schultzlab/ultra-cheap-light-field-microscope/Objective lens/UC2_20_focus_inlet_objective_mount_v8_30-200-240-266 v8.stl

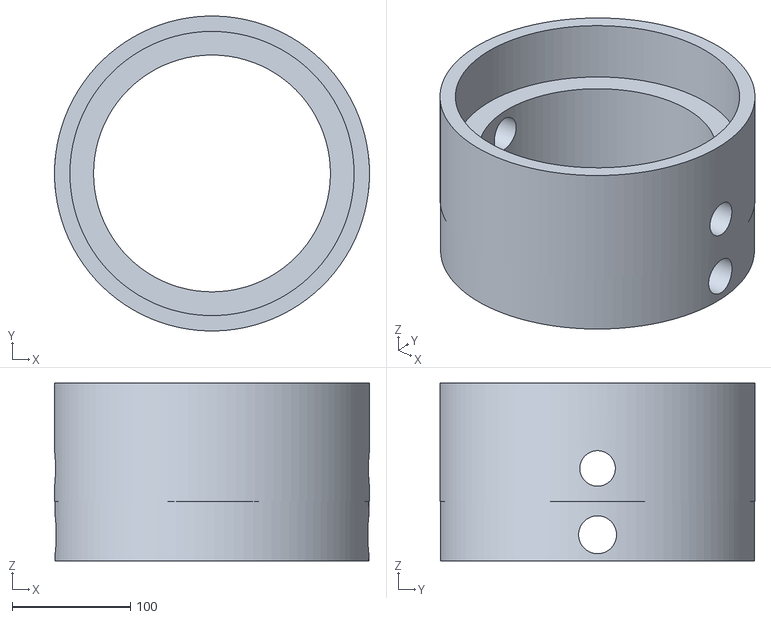
[picture p20: CAD file, 2021-07-01]
Objective lens/UC2_20_focus_inlet_objective_mount_v8_30-200-240-266 v8.stl
266.0 x 265.9 x 150.0
