schultzlab/ultra-cheap-light-field-microscope/Camera and relay lens/Cube Lid_2x1_-0.2mm with 5mm holes on one side face v1.stl

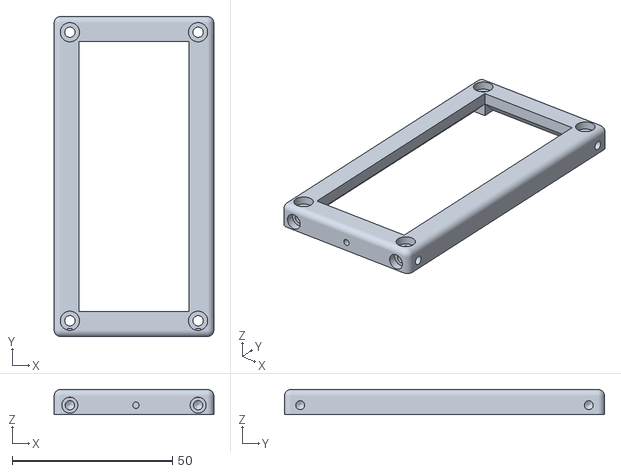
[picture p21: CAD file, 2021-07-01]
Camera and relay lens/Cube Lid_2x1_-0.2mm with 5mm holes on one side face v1.stl
49.8 x 99.8 x 7.80
