schultzlab/ultra-cheap-light-field-microscope/MLA/20_Insert_Lens_holder_v3_100mm.stl

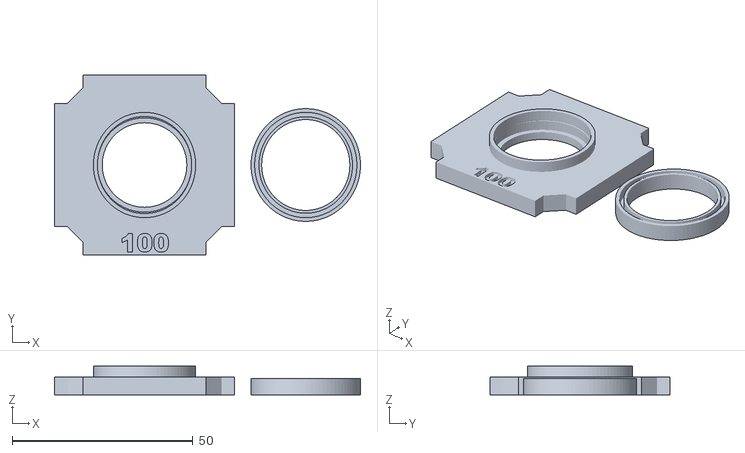
[picture p22: CAD file, 2021-07-01]
MLA/20_Insert_Lens_holder_v3_100mm.stl
84.6 x 49.8 x 8.00
