schultzlab/ultra-cheap-light-field-microscope/Modified UC2/cube for z ascii.stl

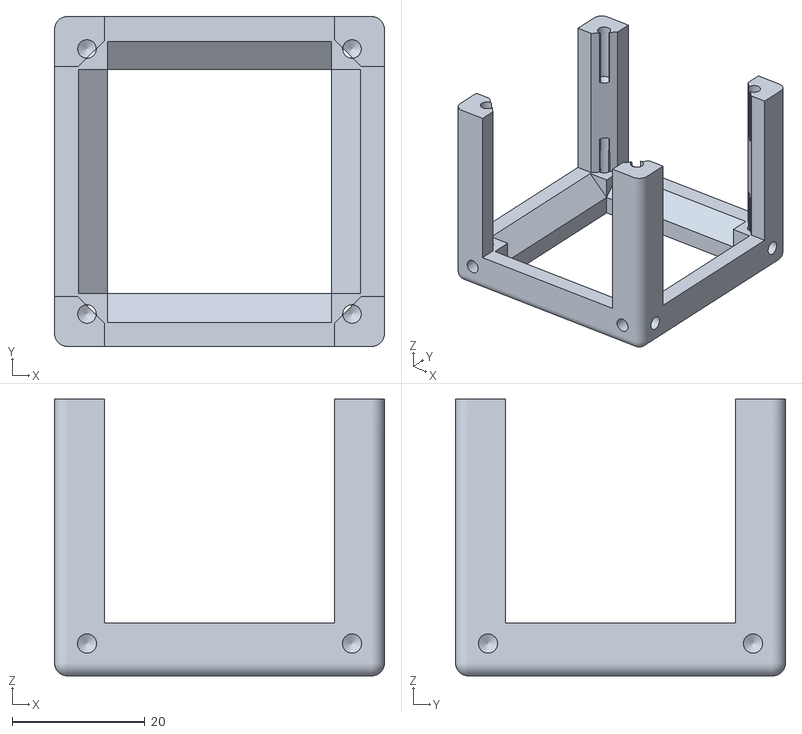
[picture p23: CAD file, 2021-07-01]
Modified UC2/cube for z ascii.stl
49.8 x 49.8 x 41.8
