schultzlab/ultra-cheap-light-field-microscope/Shortpass filter/Cube Lid_1x1 -0.1 v3.stl

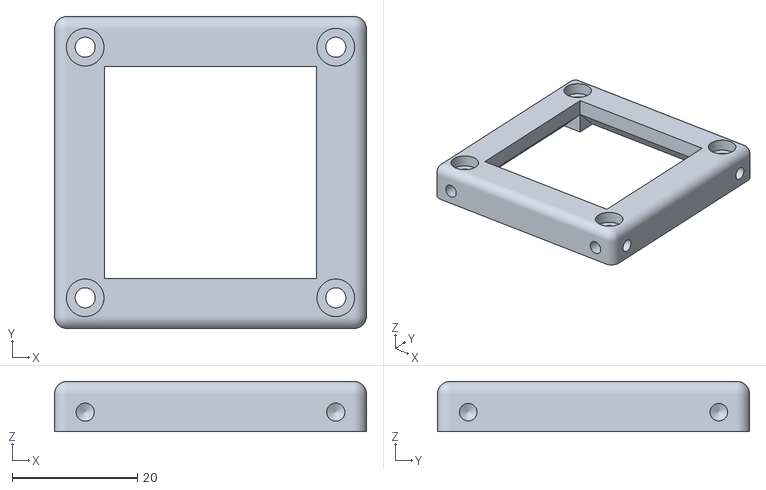
[picture p24: CAD file, 2021-07-01]
Shortpass filter/Cube Lid_1x1 -0.1 v3.stl
49.8 x 49.8 x 8.00
