schultzlab/ultra-cheap-light-field-microscope/Modified UC2/UC2_20_focus_inlet_objective_mount_v8_208-249-265 v2.stl

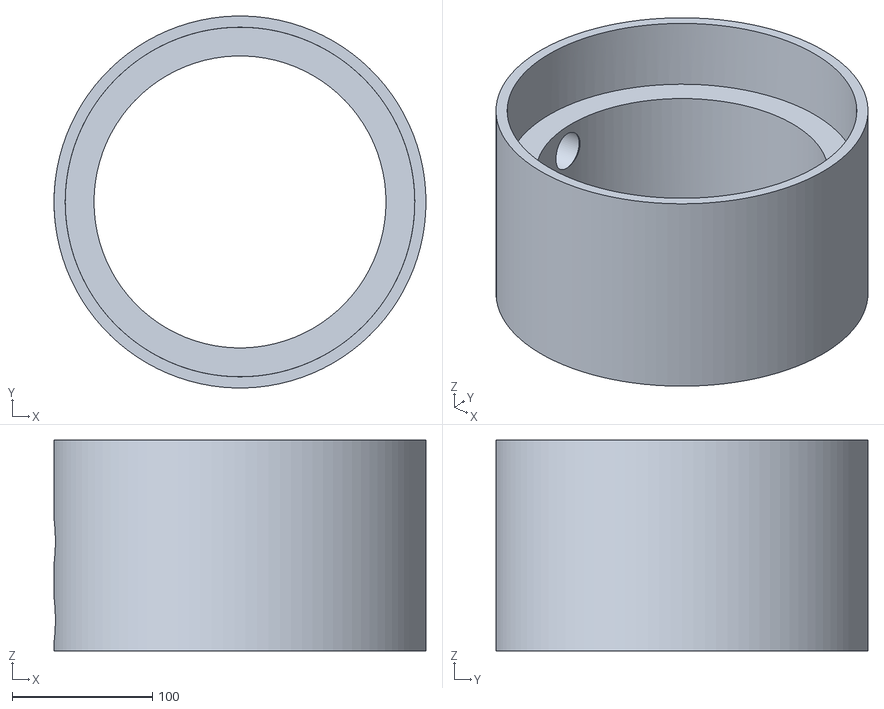
[picture p25: CAD file, 2021-07-01]
Modified UC2/UC2_20_focus_inlet_objective_mount_v8_208-249-265 v2.stl
265.0 x 264.9 x 150.0
