schultzlab/ultra-cheap-light-field-microscope/Objective lens/20_focus_inlet_linearflexure_v1_Adjusted 0.4mm v1.stl

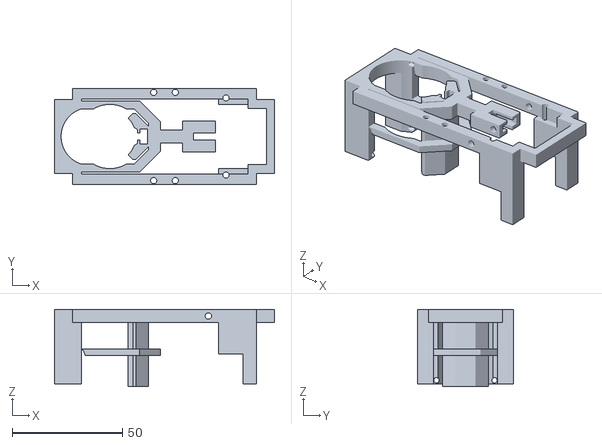
[picture p26: CAD file, 2021-07-01]
Objective lens/20_focus_inlet_linearflexure_v1_Adjusted 0.4mm v1.stl
99.8 x 43.6 x 35.0
