schultzlab/ultra-cheap-light-field-microscope/Own new parts/45 mirror_without_hole v3.stl

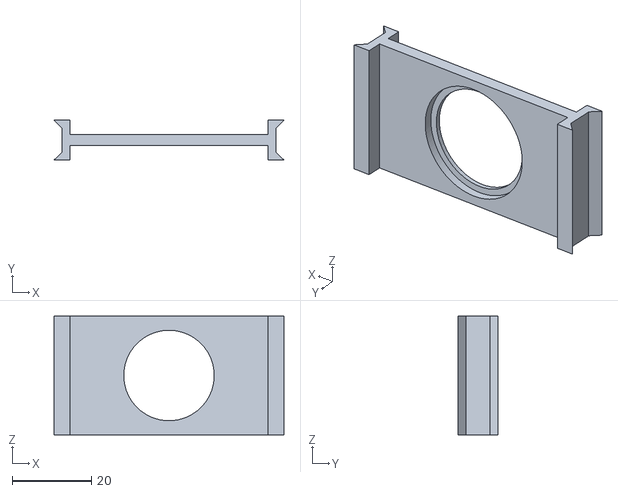
[picture p27: CAD file, 2021-07-01]
Own new parts/45 mirror_without_hole v3.stl
58.1 x 10.1 x 30.0
