schultzlab/ultra-cheap-light-field-microscope/Tube lens/SM1V05-Solidworks body 25.85.STL

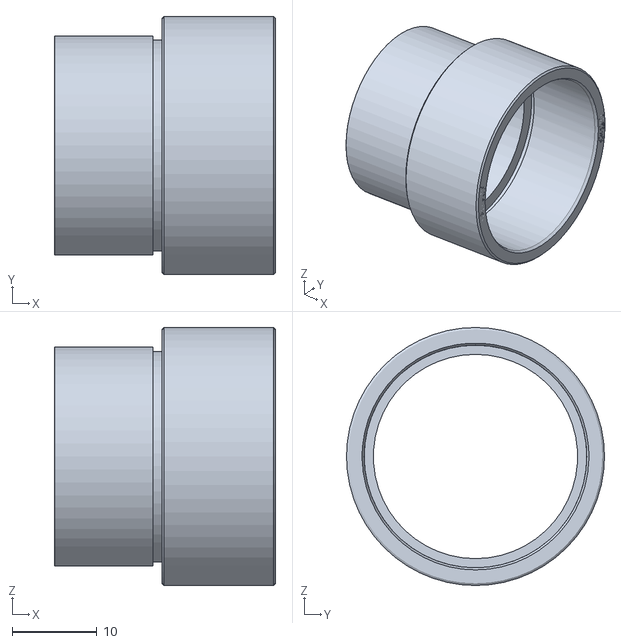
[picture p28: CAD file, 2021-07-01]
Tube lens/SM1V05-Solidworks body 25.85.STL
26.2 x 30.5 x 30.5
