schultzlab/ultra-cheap-light-field-microscope/Dichroic mirror/45 mirror_with_hole_thin_ver v1.stl

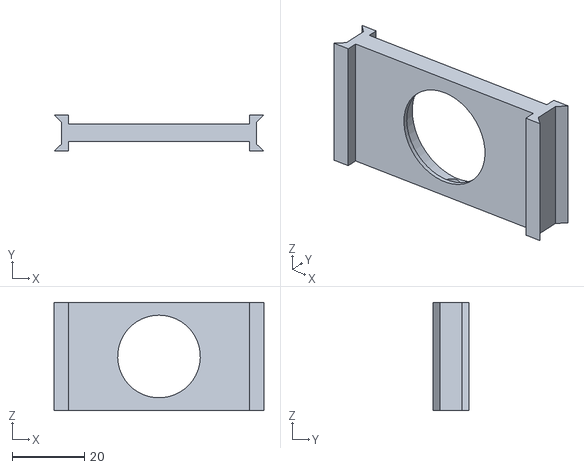
[picture p29: CAD file, 2021-07-01]
Dichroic mirror/45 mirror_with_hole_thin_ver v1.stl
58.1 x 10.1 x 30.0
