schultzlab/ultra-cheap-light-field-microscope/LED/LED HOLDER expanded v2.stl

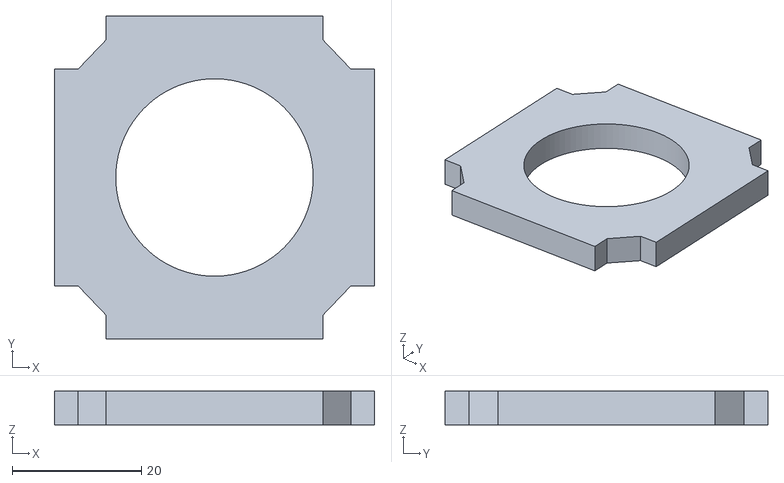
[picture p30: CAD file, 2021-07-01]
LED/LED HOLDER expanded v2.stl
49.6 x 50.0 x 5.22
