schultzlab/ultra-cheap-light-field-microscope/Modified UC2/20_Cube_Insert_Objective_Holder v4.stl

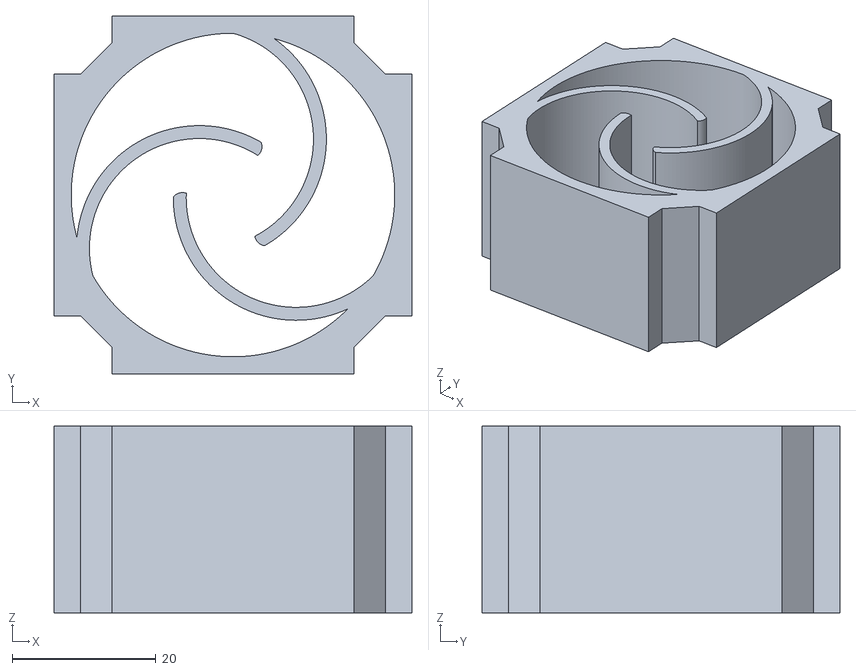
[picture p31: CAD file, 2021-07-01]
Modified UC2/20_Cube_Insert_Objective_Holder v4.stl
49.8 x 49.8 x 26.0
