schultzlab/ultra-cheap-light-field-microscope/Objective lens/UC2_20_focus_inlet_objective_mount_v8_30-202-242-270 v11.stl

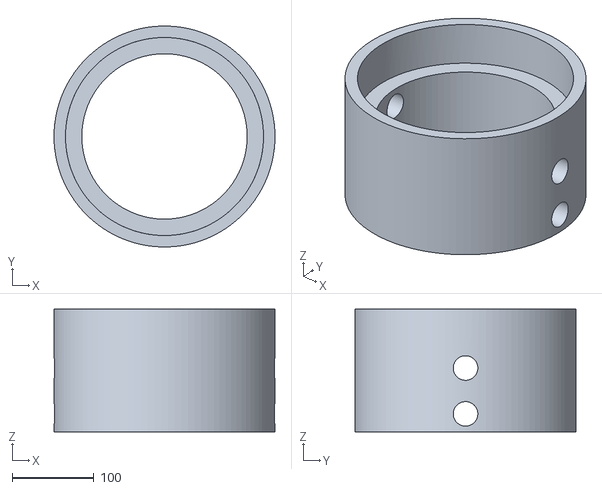
[picture p32: CAD file, 2021-07-01]
Objective lens/UC2_20_focus_inlet_objective_mount_v8_30-202-242-270 v11.stl
270.0 x 269.9 x 150.0
