schultzlab/ultra-cheap-light-field-microscope/Objective lens/UC2_v3_10_Base_puzzle_8mm_extended v2.stl

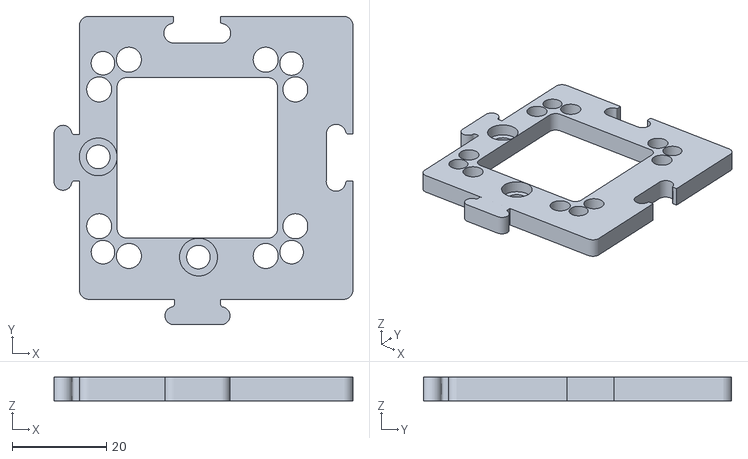
[picture p33: CAD file, 2021-07-01]
Objective lens/UC2_v3_10_Base_puzzle_8mm_extended v2.stl
63.4 x 65.4 x 5.01
