schultzlab/ultra-cheap-light-field-microscope/Tube lens/SM1V05-Solidworks 25.85.SLDPRT

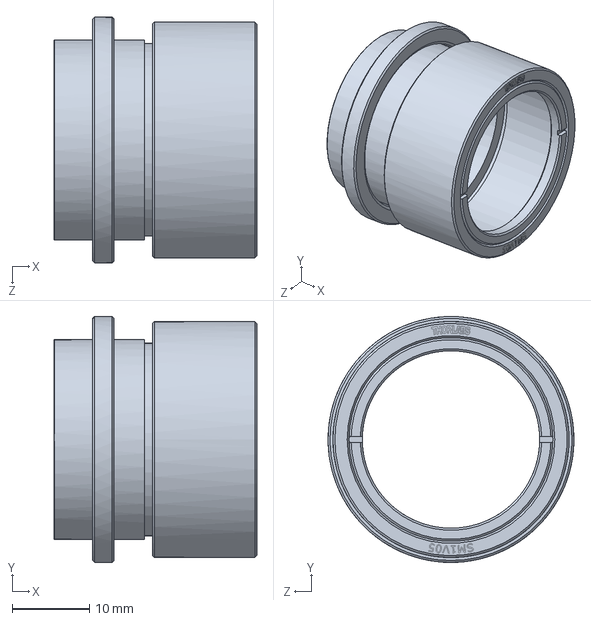
[picture p34: CAD file, 2021-07-01]
Tube lens/SM1V05-Solidworks 25.85.SLDPRT
26.2 x 31.7 x 31.7 mm
