schultzlab/ultra-cheap-light-field-microscope/Tube lens/SM1RR-Solidworks.sldprt

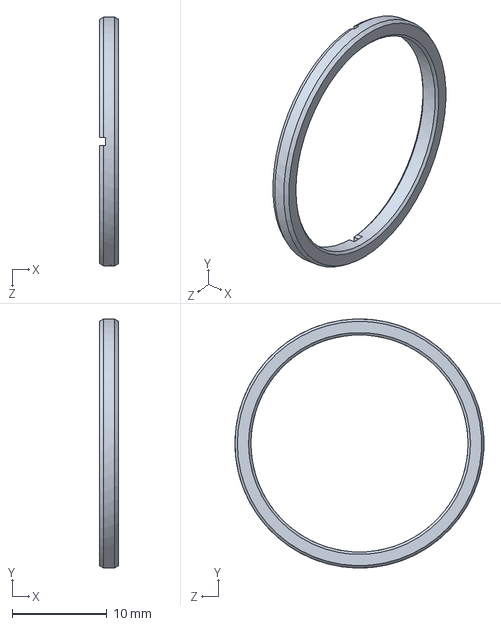
[picture p35: CAD file, 2021-07-01]
Tube lens/SM1RR-Solidworks.sldprt
2.03 x 26.3 x 26.3 mm
