schultzlab/ultra-cheap-light-field-microscope/Modified UC2/10_Lid_2x1_v3 v2.stl

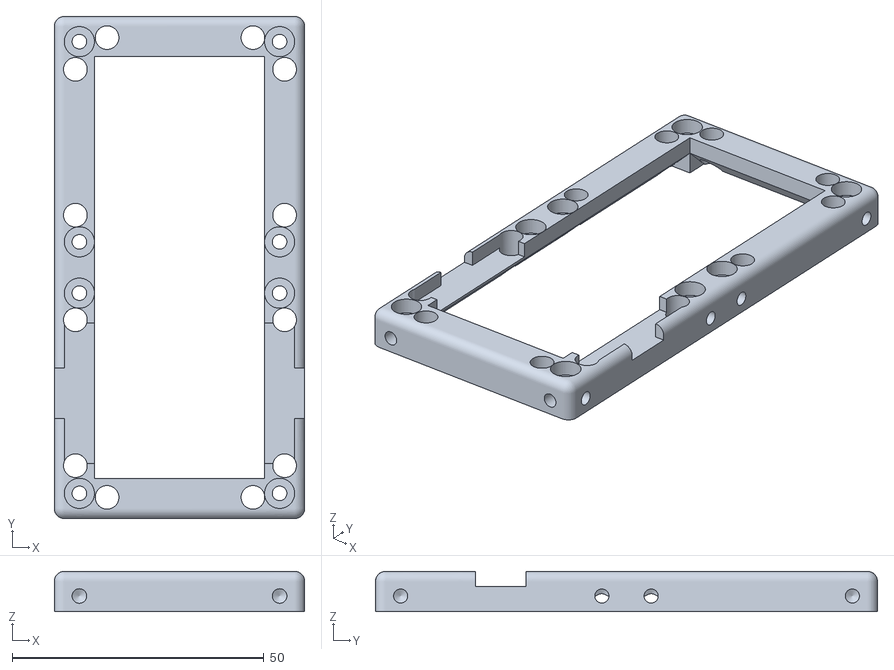
[picture p36: CAD file, 2021-07-01]
Modified UC2/10_Lid_2x1_v3 v2.stl
49.8 x 99.8 x 8.00
