schultzlab/ultra-cheap-light-field-microscope/Own new parts/45 mirror.SLDPRT

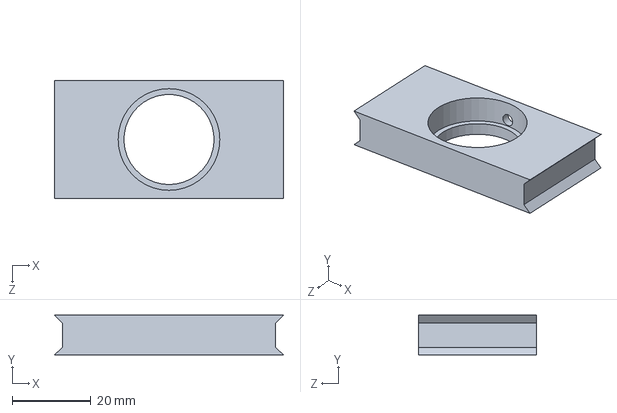
[picture p37: CAD file, 2021-07-01]
Own new parts/45 mirror.SLDPRT
58.1 x 10.1 x 30.0 mm
