schultzlab/ultra-cheap-light-field-microscope/Objective lens/Cube Lid_1x1 with 5mm holes on one side face v1.stl

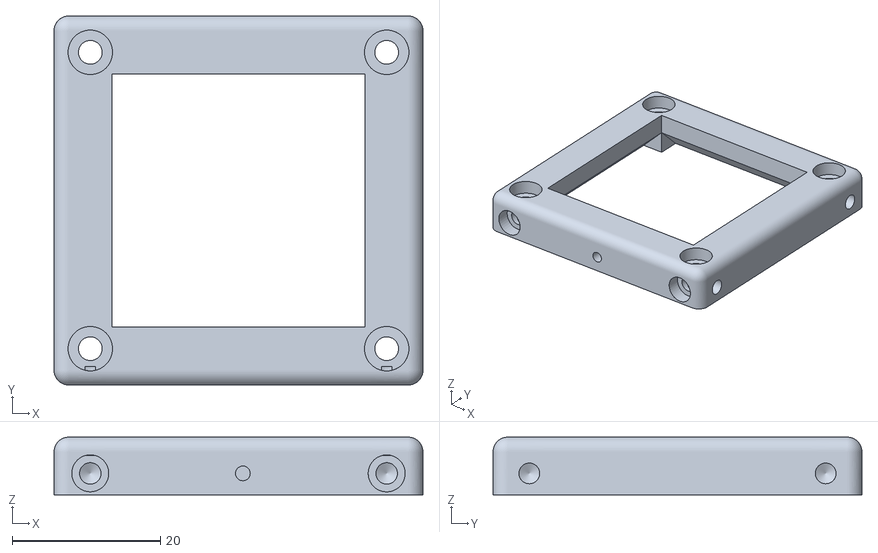
[picture p38: CAD file, 2021-07-01]
Objective lens/Cube Lid_1x1 with 5mm holes on one side face v1.stl
49.8 x 49.8 x 7.80
