schultzlab/ultra-cheap-light-field-microscope/Modified UC2/30_alignment_template_5.217mm_lens_insert v2.stl

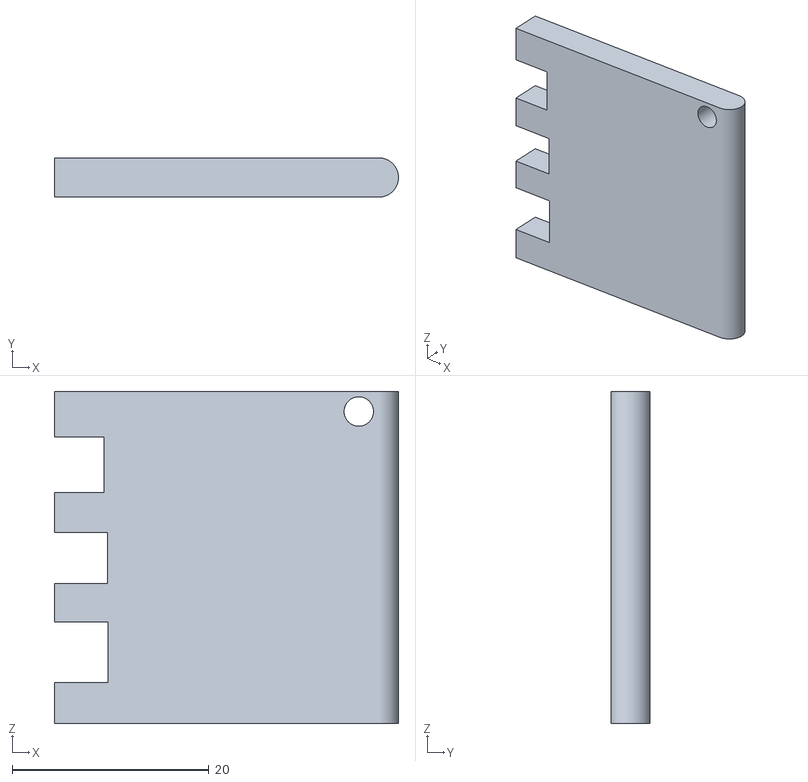
[picture p39: CAD file, 2021-07-01]
Modified UC2/30_alignment_template_5.217mm_lens_insert v2.stl
35.0 x 4.00 x 33.8
