schultzlab/ultra-cheap-light-field-microscope/Objective lens/UC2_20_focus_inlet_objective_mount_v8_30-202-242-268_v13.stl

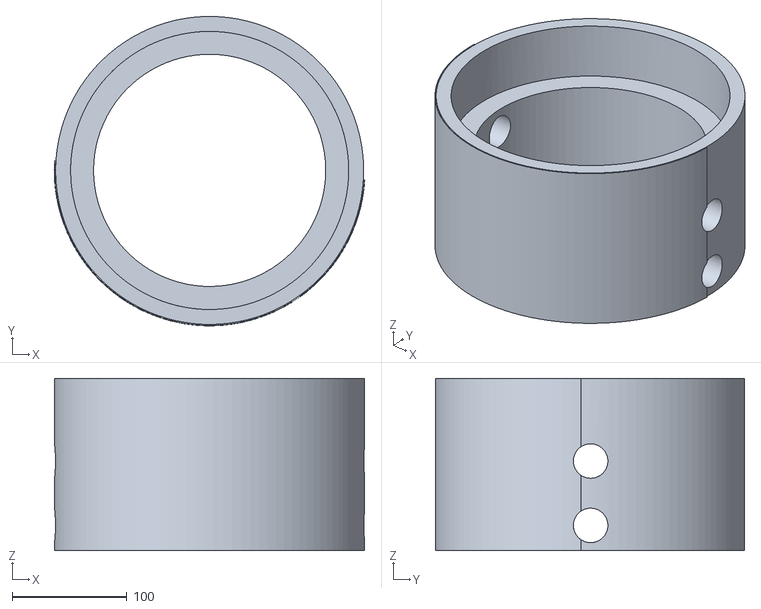
[picture p40: CAD file, 2021-07-01]
Objective lens/UC2_20_focus_inlet_objective_mount_v8_30-202-242-268_v13.stl
269.7 x 268.9 x 150.0
