schultzlab/ultra-cheap-light-field-microscope/Modified UC2/20_Cube_Insert_RaspiCam2.0 v9.stl

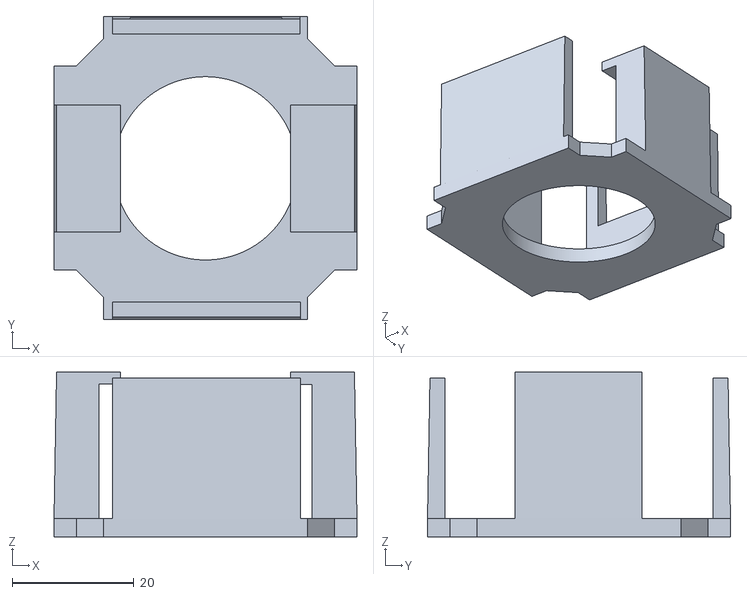
[picture p41: CAD file, 2021-07-01]
Modified UC2/20_Cube_Insert_RaspiCam2.0 v9.stl
49.8 x 49.8 x 27.1
