schultzlab/ultra-cheap-light-field-microscope/Modified UC2/10_Cube_2x1_-0.1mm_marked v1.stl

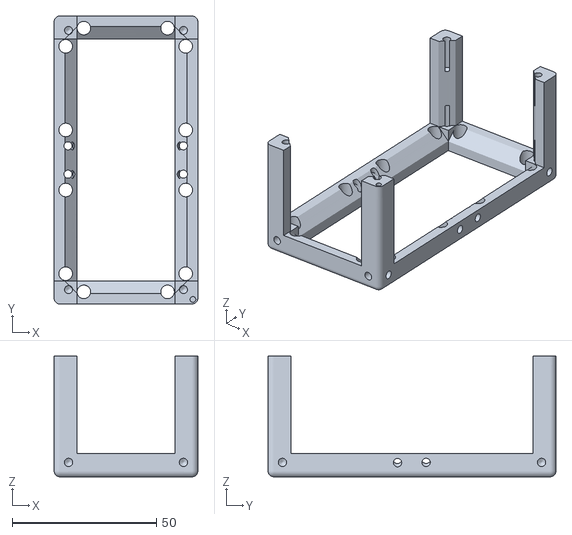
[picture p42: CAD file, 2021-07-01]
Modified UC2/10_Cube_2x1_-0.1mm_marked v1.stl
49.8 x 99.8 x 41.8
