schultzlab/ultra-cheap-light-field-microscope/Modified UC2/UC2_30_printing_calibrator_v3.stl

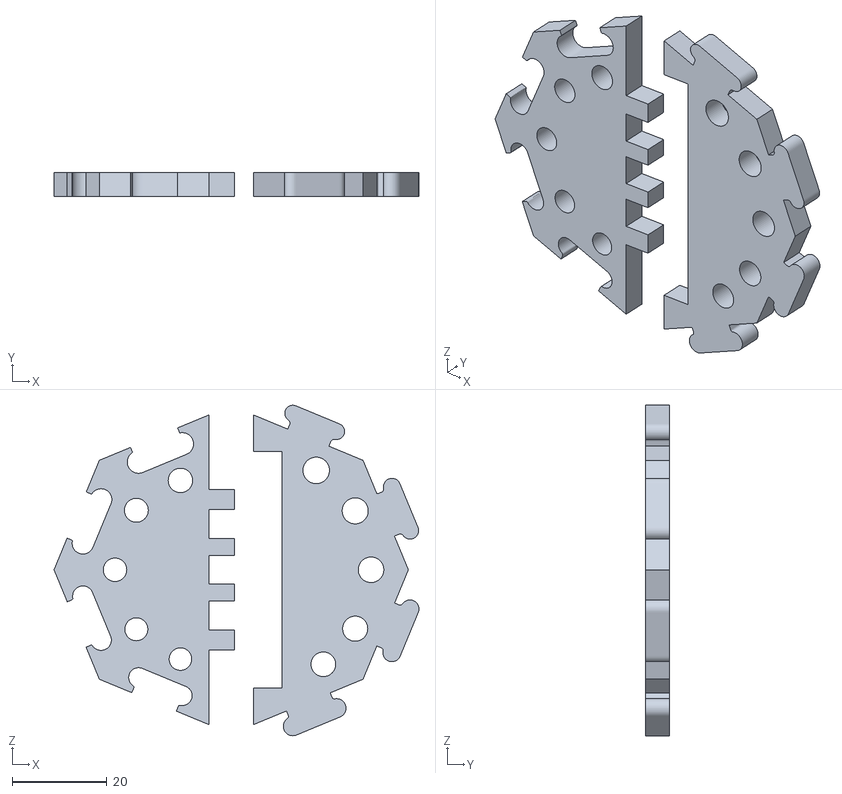
[picture p43: CAD file, 2021-07-01]
Modified UC2/UC2_30_printing_calibrator_v3.stl
77.0 x 5.00 x 69.7
