schultzlab/ultra-cheap-light-field-microscope/Modified UC2/Cube_1x1 -0.25mm.stl

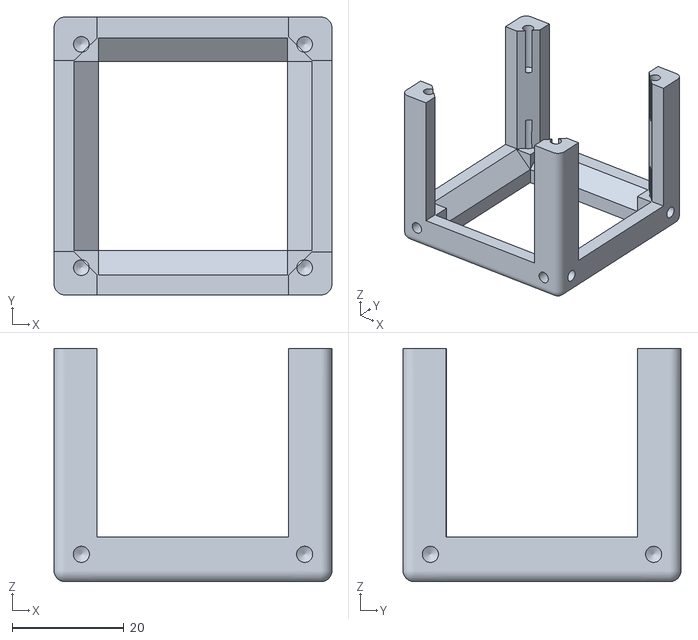
[picture p45: CAD file, 2021-07-01]
Modified UC2/Cube_1x1 -0.25mm.stl
49.8 x 49.8 x 41.8
