schultzlab/ultra-cheap-light-field-microscope/Modified UC2/10_Base_v2 v2.stl

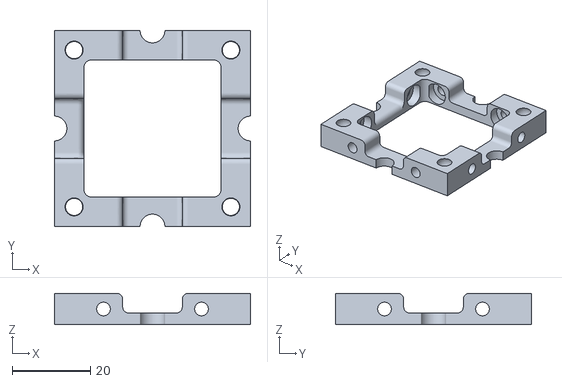
[picture p46: CAD file, 2021-07-01]
Modified UC2/10_Base_v2 v2.stl
50.0 x 50.0 x 8.00
