schultzlab/ultra-cheap-light-field-microscope/Modified UC2/UC2_20_focus_inlet_objective_mount_v8_205-243 v1.stl

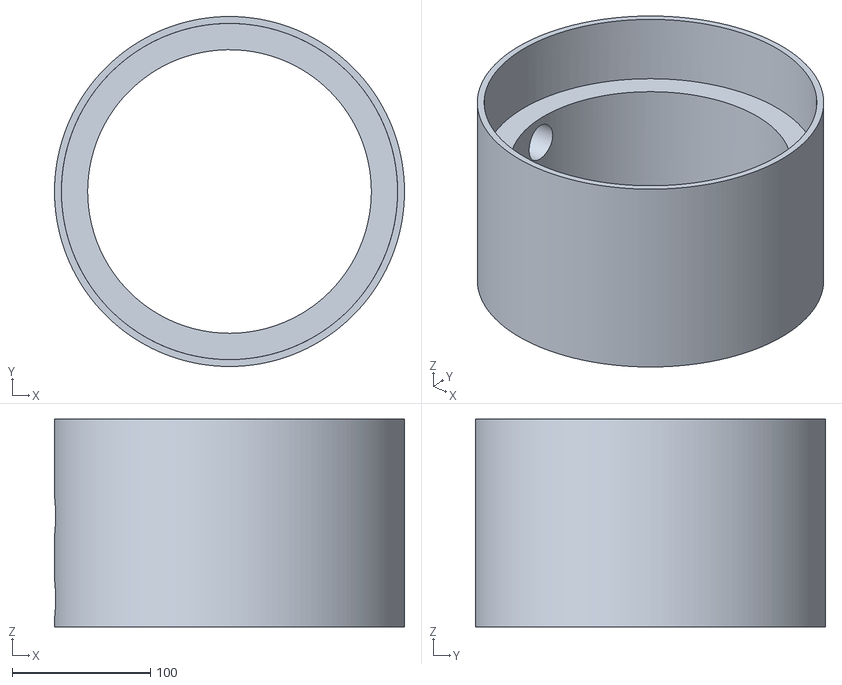
[picture p47: CAD file, 2021-07-01]
Modified UC2/UC2_20_focus_inlet_objective_mount_v8_205-243 v1.stl
253.0 x 253.0 x 150.0
