schultzlab/ultra-cheap-light-field-microscope/Modified UC2/00_Connector_Baseplate v1.stl

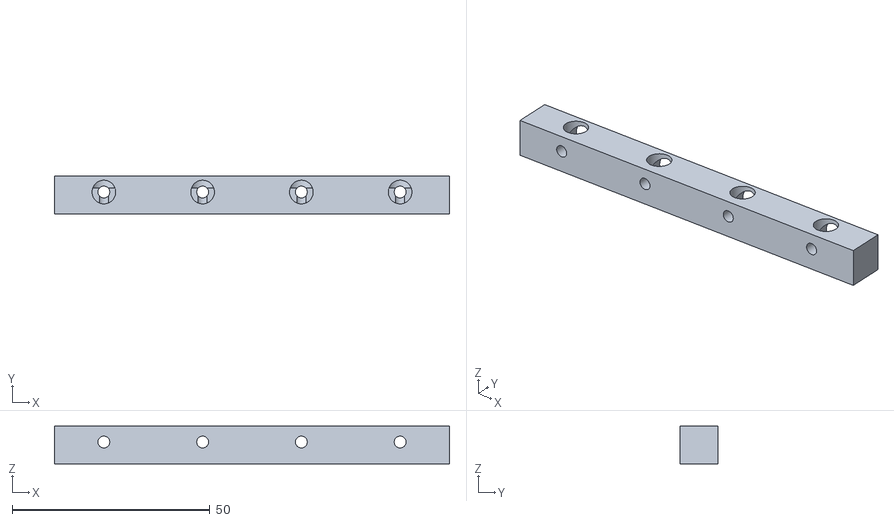
[picture p48: CAD file, 2021-07-01]
Modified UC2/00_Connector_Baseplate v1.stl
100.0 x 9.50 x 9.50
