schultzlab/ultra-cheap-light-field-microscope/Modified UC2/Objective_mount_202 v1.stl

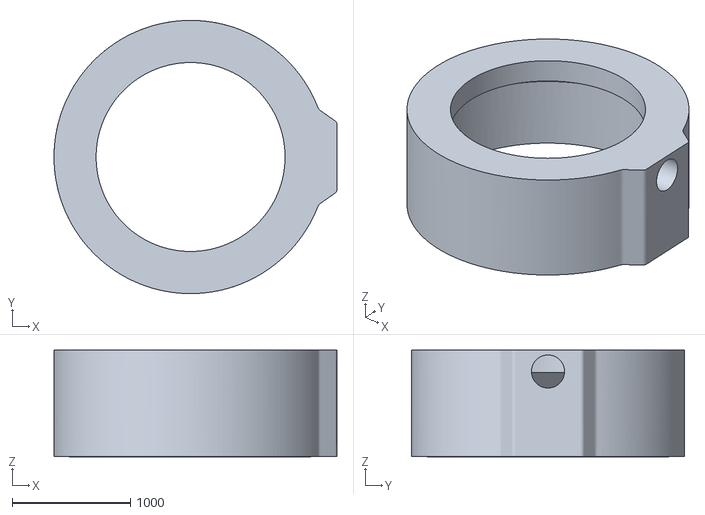
[picture p50: CAD file, 2021-07-01]
Modified UC2/Objective_mount_202 v1.stl
2396.9 x 2313.9 x 902.5
