schultzlab/ultra-cheap-light-field-microscope/Modified UC2/UC2_20_focus_inlet_linearflexure_mechanical_v3 v3.stl

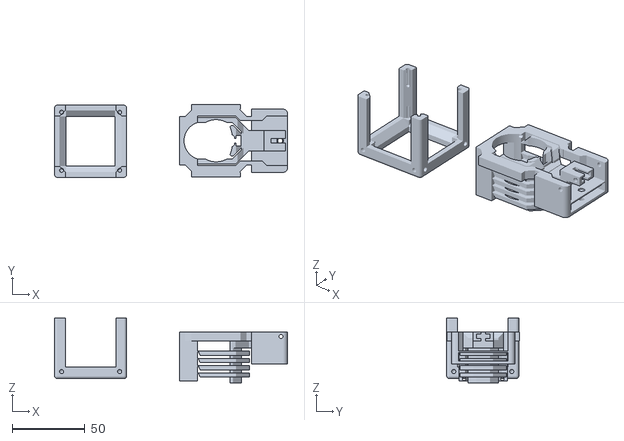
[picture p51: CAD file, 2021-07-01]
Modified UC2/UC2_20_focus_inlet_linearflexure_mechanical_v3 v3.stl
160.7 x 50.1 x 44.7
