schultzlab/ultra-cheap-light-field-microscope/Modified UC2/20_Cube_Insert_Z-Focus_3.2mm v2.stl

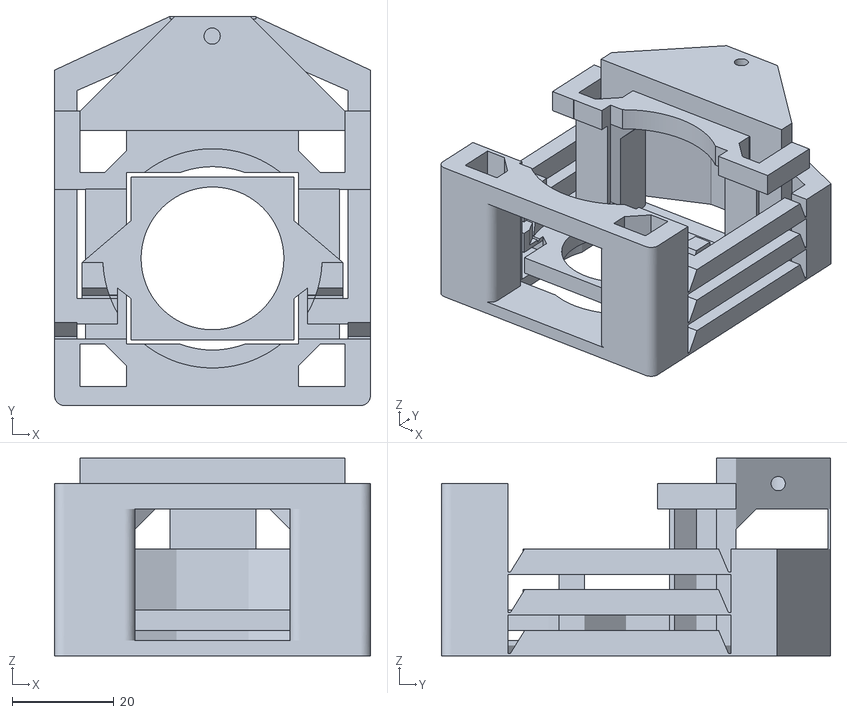
[picture p52: CAD file, 2021-07-01]
Modified UC2/20_Cube_Insert_Z-Focus_3.2mm v2.stl
62.0 x 76.4 x 38.8
